marianoelia/IoT-nixie-clock/BoardFiles/BottomBoard/Board.png

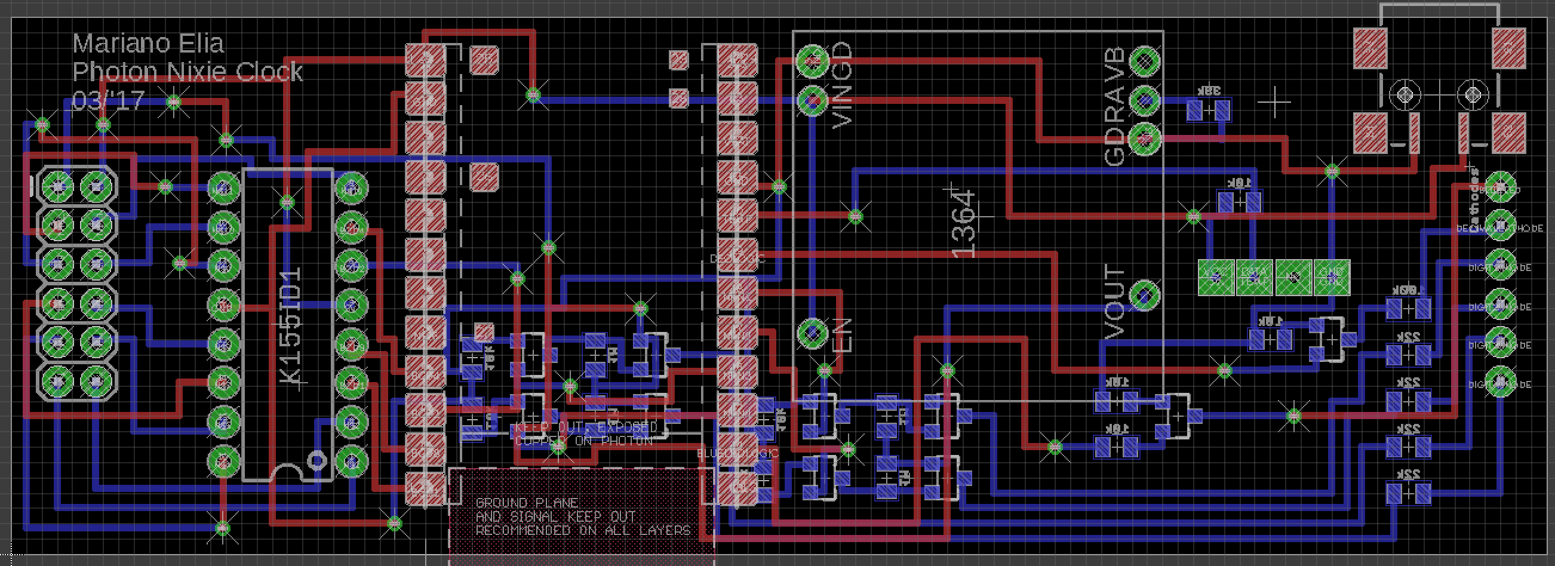
BoardFiles/BottomBoard/Board.png
