marianoelia/IoT-nixie-clock/BoardFiles/TopBoard/Board.png

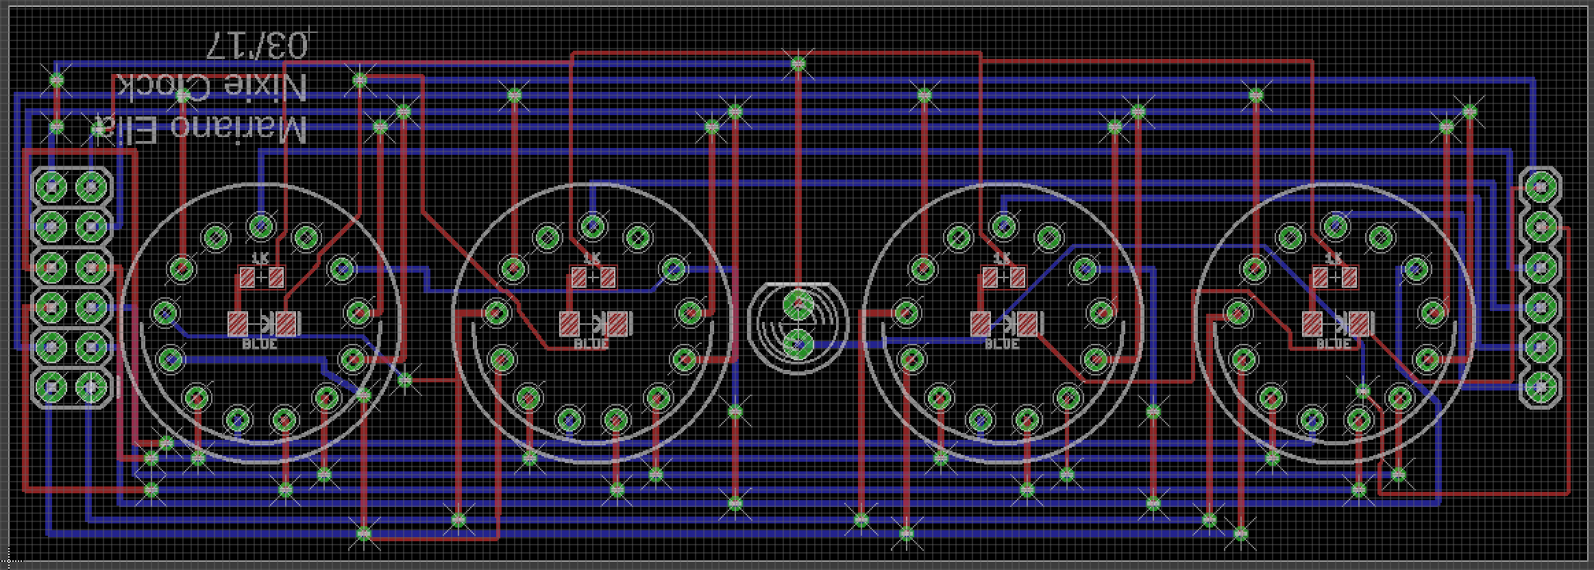
BoardFiles/TopBoard/Board.png
