marianoelia/IoT-nixie-clock/Extra/Pictures/AnnotatedBreadboard.jpg

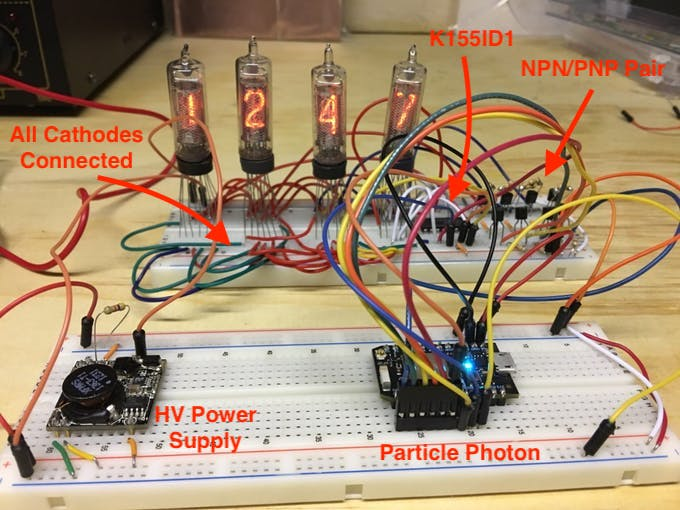
Extra/Pictures/AnnotatedBreadboard.jpg
