marianoelia/IoT-nixie-clock/Extra/Pictures/NixieClockWarmLight.JPG

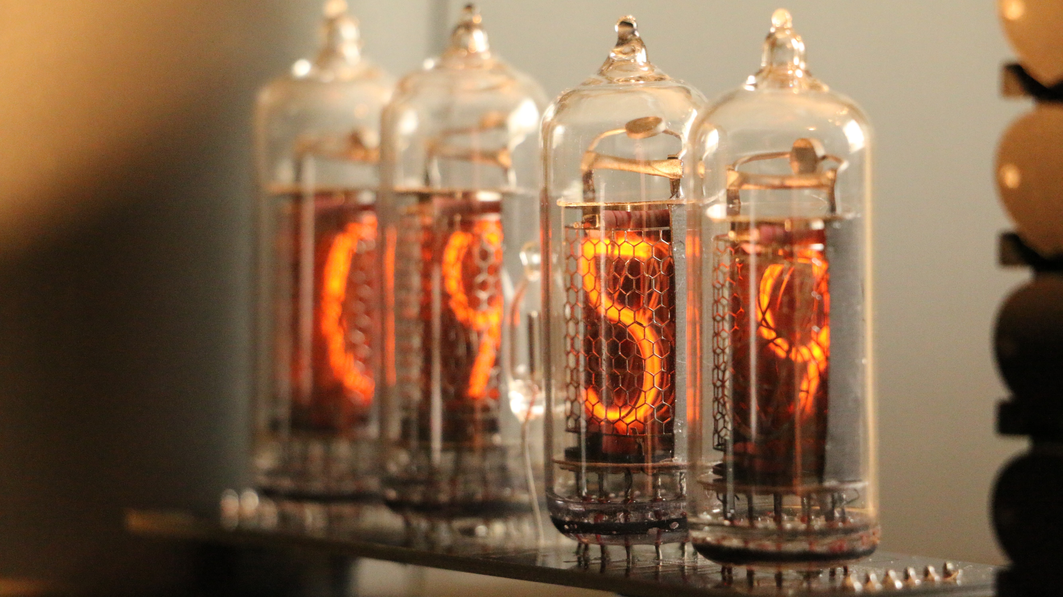
Extra/Pictures/NixieClockWarmLight.JPG
